s-light/magic_amulet/pattern_ideas/3seile_geflochten.jpg

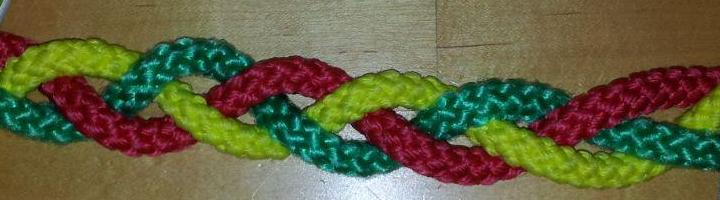
pattern_ideas/3seile_geflochten.jpg
