s-light/magic_amulet/export/front_layers/front_layer_3.dxf

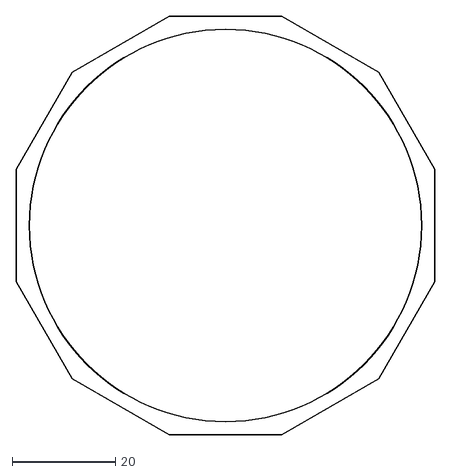
[picture p29: CAD file, 2019-01-21]
export/front_layers/front_layer_3.dxf
81.1 x 81.1
