s-light/magic_amulet/export/alu_layers/alu_layer_1.dxf

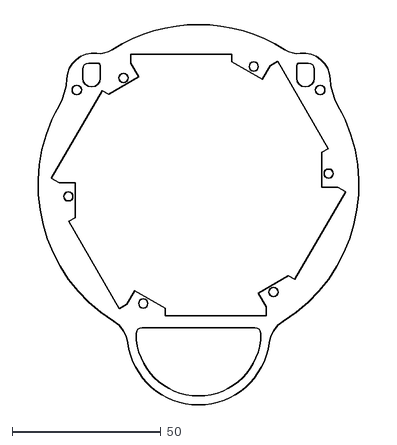
[picture p30: CAD file, 2019-01-24]
export/alu_layers/alu_layer_1.dxf
122.6 x 130.8
