s-light/magic_amulet/export/back_layers/back_layer_2.dxf

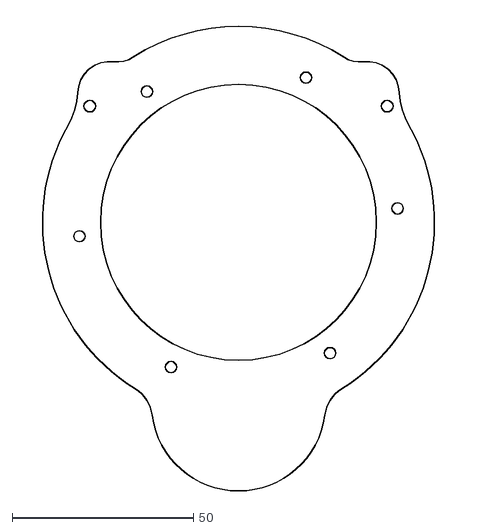
[picture p31: CAD file, 2019-01-24]
export/back_layers/back_layer_2.dxf
122.6 x 130.8
