s-light/magic_amulet/export/front_layers/front_layer_1_in.dxf

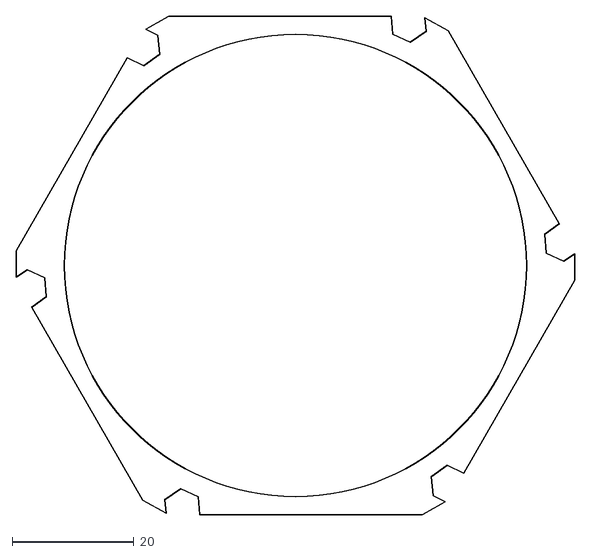
[picture p32: CAD file, 2019-01-21]
export/front_layers/front_layer_1_in.dxf
91.9 x 82.0
