s-light/magic_amulet/export/in_back.dxf

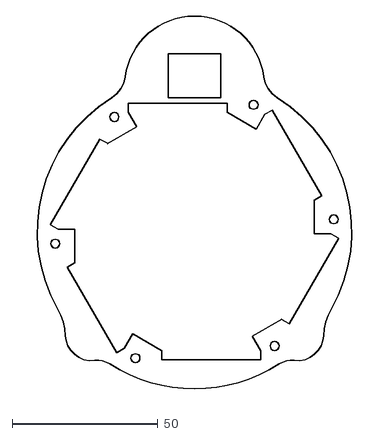
[picture p33: CAD file, 2018-10-28]
export/in_back.dxf
122.6 x 130.8
