s-light/magic_amulet/led_soldering_helper.dxf

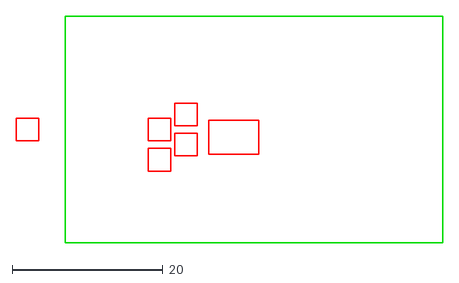
[picture p34: CAD file, 2018-09-11]
led_soldering_helper.dxf
56.5 x 30.0
