s-light/magic_amulet/export/alu_layers/alu_layer_0.dxf

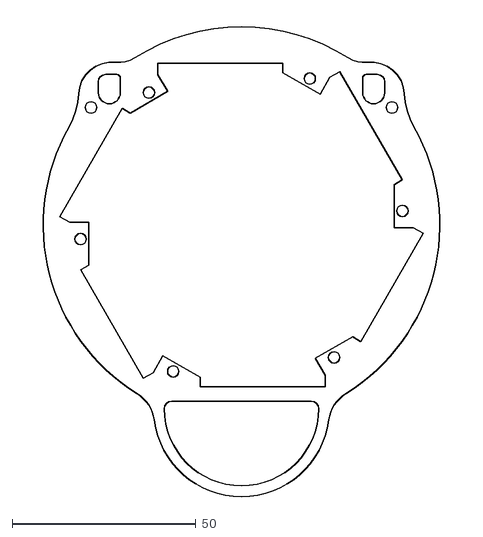
[picture p35: CAD file, 2019-01-24]
export/alu_layers/alu_layer_0.dxf
122.6 x 130.8
