s-light/magic_amulet/export/front_layers/front_layer_2.dxf

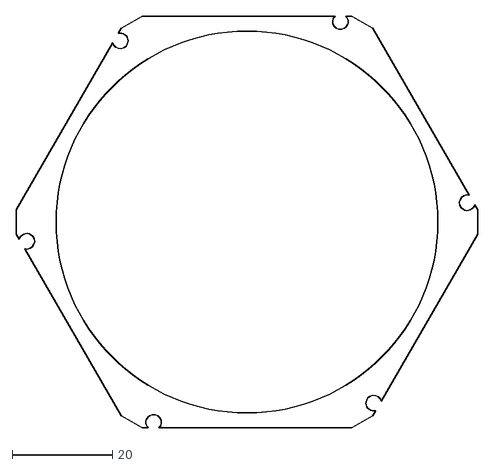
[picture p36: CAD file, 2019-01-21]
export/front_layers/front_layer_2.dxf
91.9 x 82.0
