s-light/magic_amulet/export/in_front.dxf

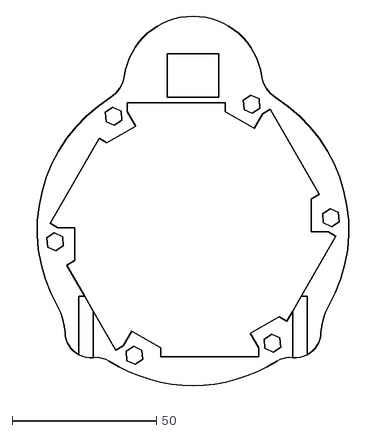
[picture p37: CAD file, 2018-10-28]
export/in_front.dxf
122.6 x 130.8
