s-light/magic_amulet/export/front.dxf

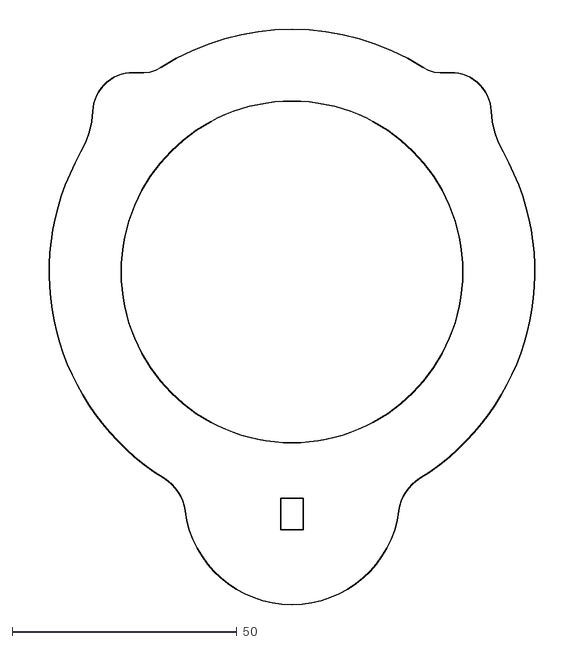
[picture p38: CAD file, 2018-10-28]
export/front.dxf
122.6 x 130.8
