s-light/magic_amulet/export/front_layers/front_layer_1_out.dxf

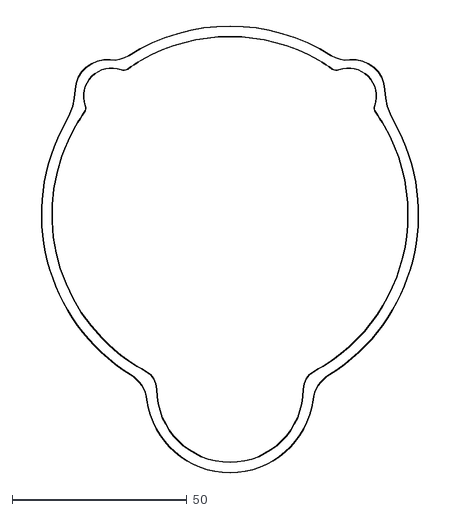
[picture p39: CAD file, 2019-01-21]
export/front_layers/front_layer_1_out.dxf
122.6 x 130.8
