s-light/magic_amulet/export/back.dxf

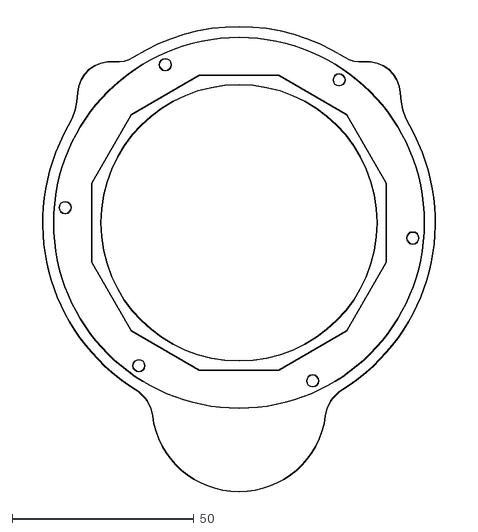
[picture p40: CAD file, 2018-10-28]
export/back.dxf
122.6 x 130.8
