s-light/magic_amulet/export/plexiglas_L4_fill.dxf

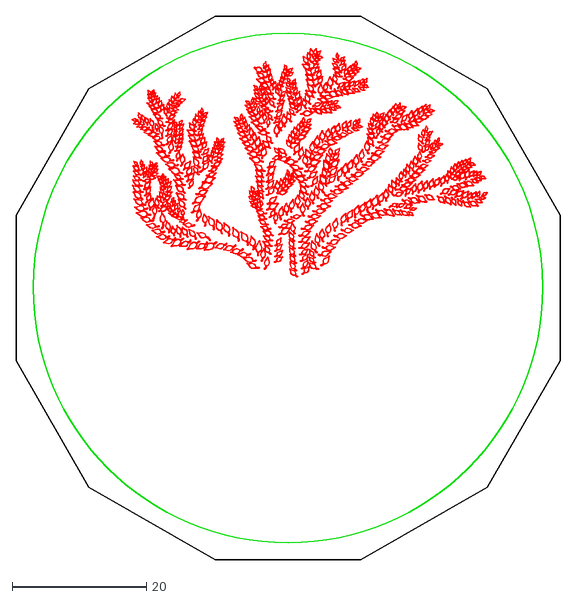
[picture p41: CAD file, 2018-10-21]
export/plexiglas_L4_fill.dxf
81.1 x 81.1
