s-light/magic_amulet/export/plexiglas_L3.dxf

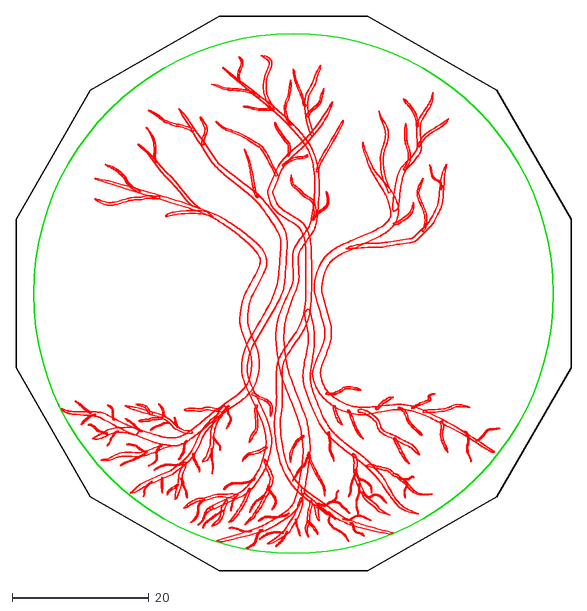
[picture p42: CAD file, 2018-10-20]
export/plexiglas_L3.dxf
81.1 x 81.1
