s-light/magic_amulet/export/plexiglas_L1.dxf

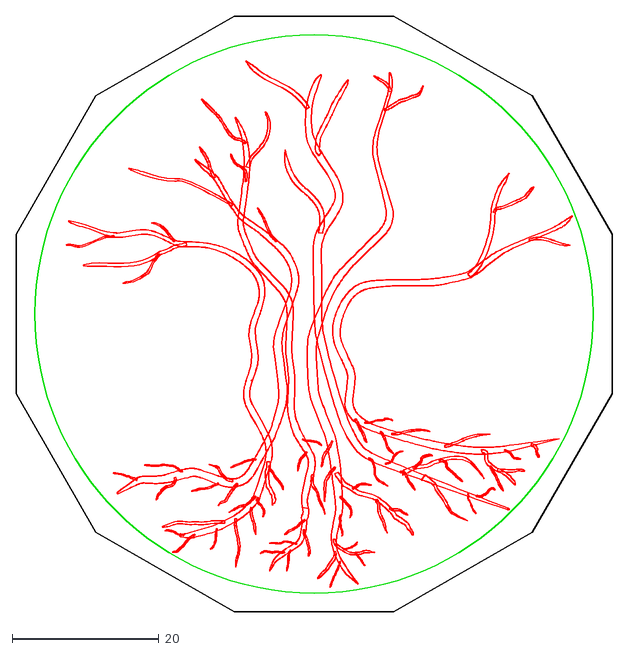
[picture p43: CAD file, 2018-10-20]
export/plexiglas_L1.dxf
81.1 x 81.1
