s-light/magic_amulet/export/plexiglas.dxf

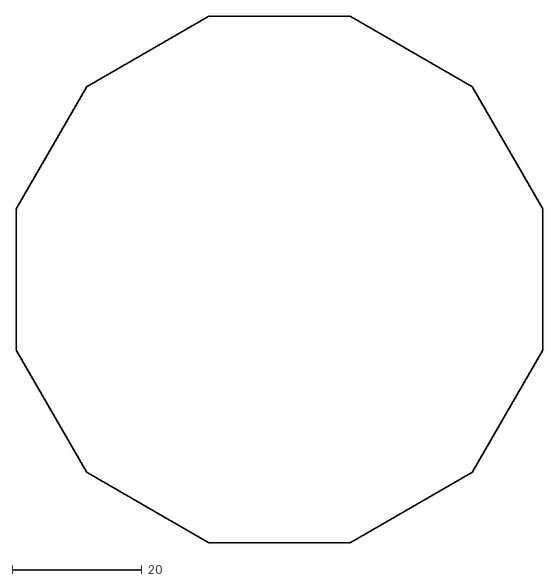
[picture p44: CAD file, 2018-10-20]
export/plexiglas.dxf
81.1 x 81.1
