s-light/magic_amulet/export/plexiglas_L2_fill.dxf

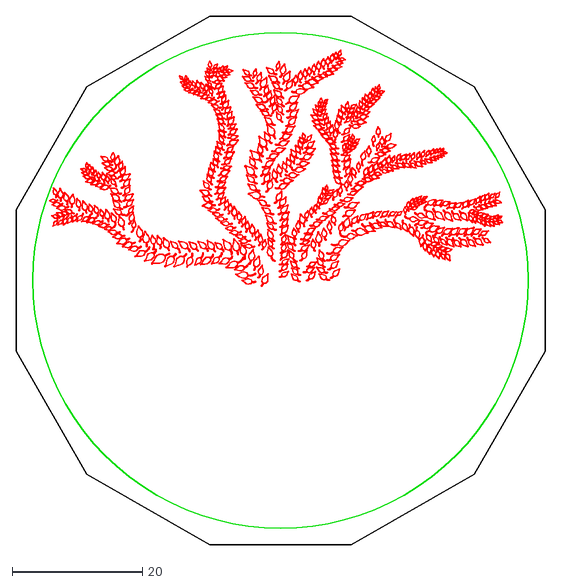
[picture p45: CAD file, 2018-10-20]
export/plexiglas_L2_fill.dxf
81.1 x 81.1
