s-light/magic_amulet/export/plexiglas_L4.dxf

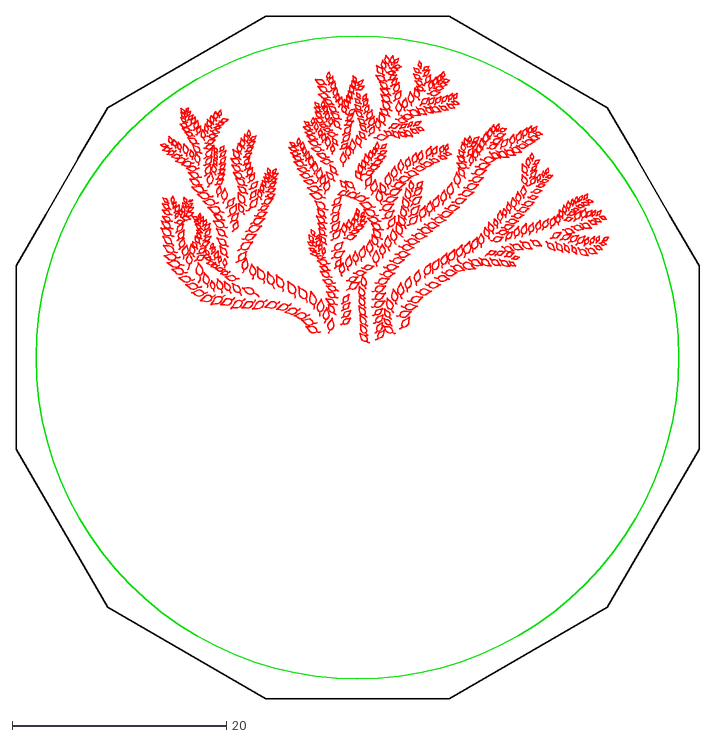
[picture p46: CAD file, 2018-09-11]
export/plexiglas_L4.dxf
63.8 x 63.8
