s-light/magic_amulet/export/plexiglas_L2.dxf

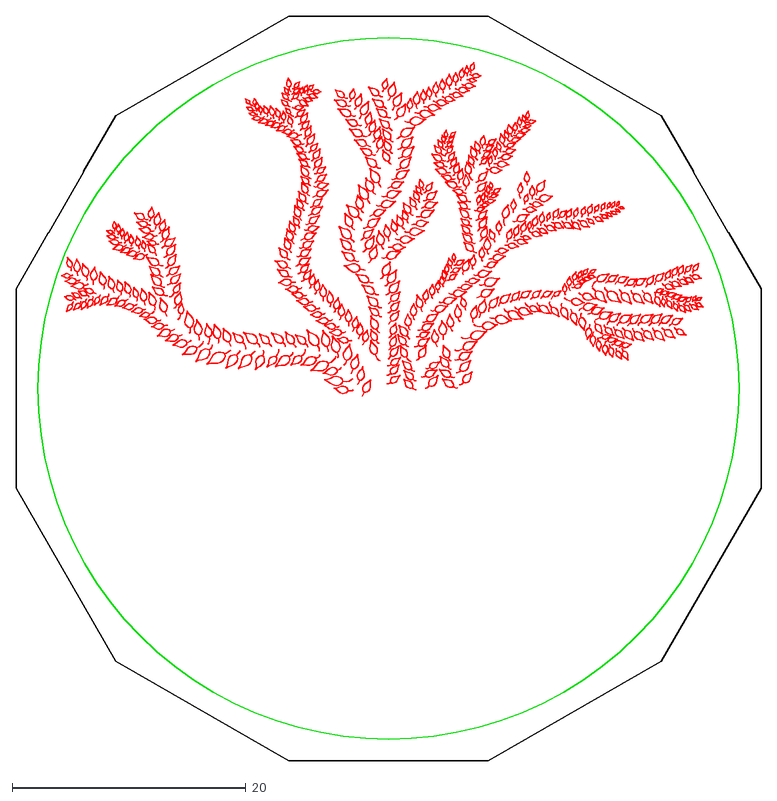
[picture p47: CAD file, 2018-09-11]
export/plexiglas_L2.dxf
63.8 x 63.8
